MuhammadNauvalDwiAfandi/DiagnosisByTouch/Documentation/DS18B20/WhatsApp Image 2022-07-23 at 3.20.33 PM (1).jpeg

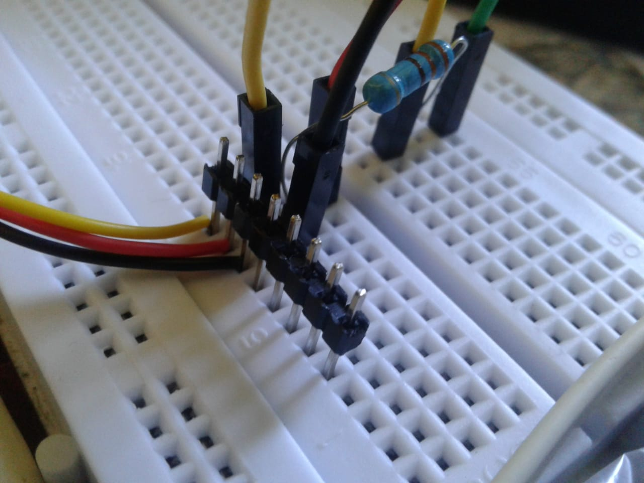
Documentation/DS18B20/WhatsApp Image 2022-07-23 at 3.20.33 PM (1).jpeg
