MuhammadNauvalDwiAfandi/DiagnosisByTouch/Documentation/LED/20220728_161453.jpg

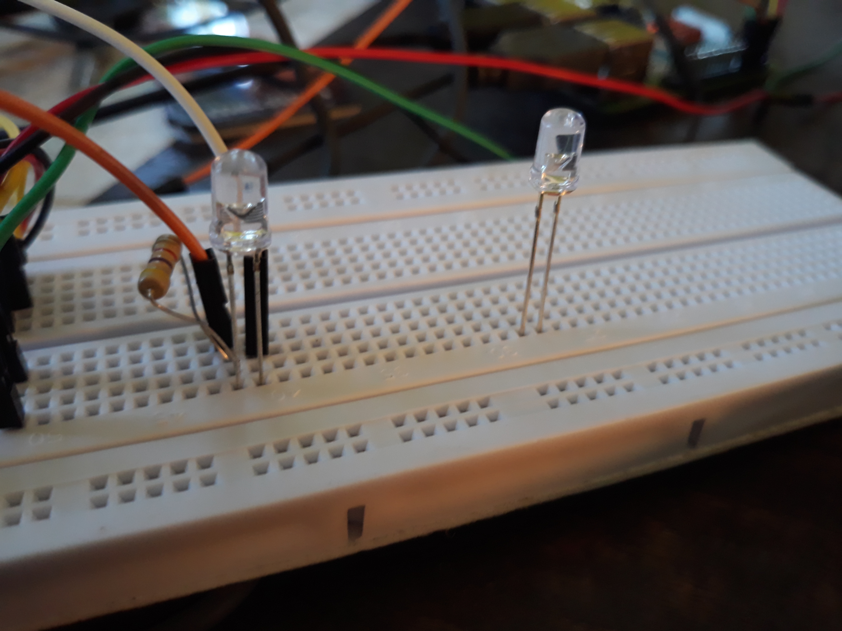
Documentation/LED/20220728_161453.jpg
