MuhammadNauvalDwiAfandi/DiagnosisByTouch/TestScript/mainOksi.py

import time

import max30102
import hrcalc

m = max30102.MAX30102()

def Oksi(devStatus):
    hr2 = 0
    sp2 = 0
    red, ir = m.read_sequential()
    
    hr,hrb,sp,spb = hrcalc.calc_hr_and_spo2(ir, red)

    if devStatus:

        print("hr detected:",hrb)
        print("sp detected:",spb)
        
        if(hrb == True and hr != -999):
            hr2 = int(hr)
            print("Heart Rate : ",hr2)
        if(spb == True and sp != -999):
            sp2 = int(sp)
            print("SPO2       : ",sp2)

    return hr2, sp2, hrb, spb

if __name__ == '__main__':
    while True:

        Oksi(False)
        print('Tunggu 2 menit...')
        time.sleep(60)
        print('1 menit lagi...')
        time.sleep(30)
        print('30 detik lagi...')
        time.sleep(30)
        Oksi(True)
