MuhammadNauvalDwiAfandi/DiagnosisByTouch/TestScript/testLCD.py

from signal import signal, SIGTERM, SIGHUP, pause
from rpi_lcd import LCD
lcd = LCD()
def safe_exit(signum, frame):
    exit(1)
try:
    signal(SIGTERM, safe_exit)
    signal(SIGHUP, safe_exit)
    lcd.text("Hello,", 1)
    lcd.text("Raspberry Pi!", 2)
    pause()
except KeyboardInterrupt:
    pass
finally:
    lcd.clear()

'''
lcd.text('text to show', number of line (1-2))
'''
